hieu0902/Digital-Logic-Final/7408.jpg

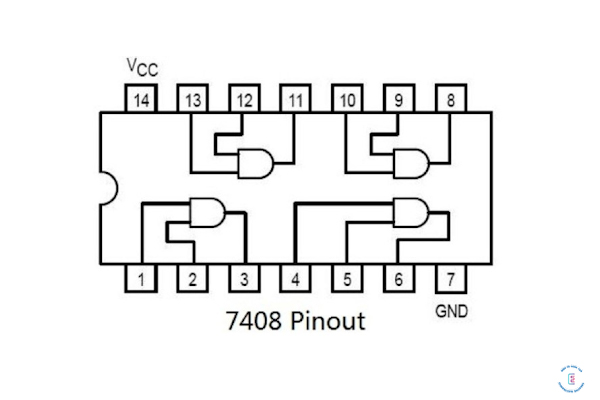
7408.jpg
