hieu0902/Digital-Logic-Final/7410.gif

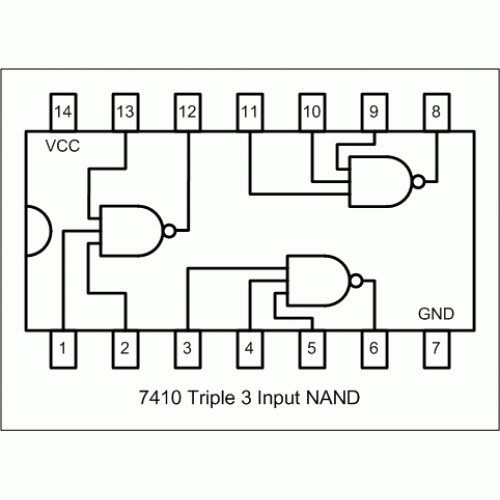
7410.gif
