hieu0902/Digital-Logic-Final/7411.png

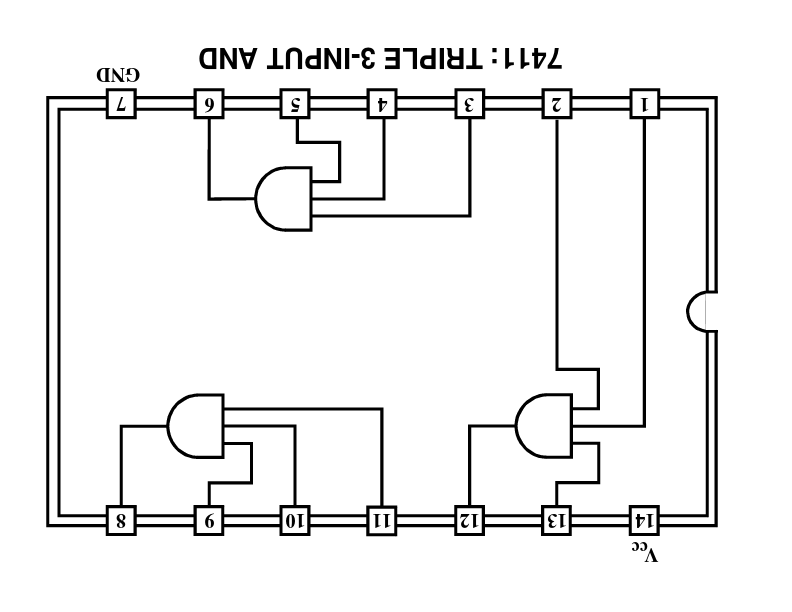
7411.png
