hieu0902/Digital-Logic-Final/7414.png

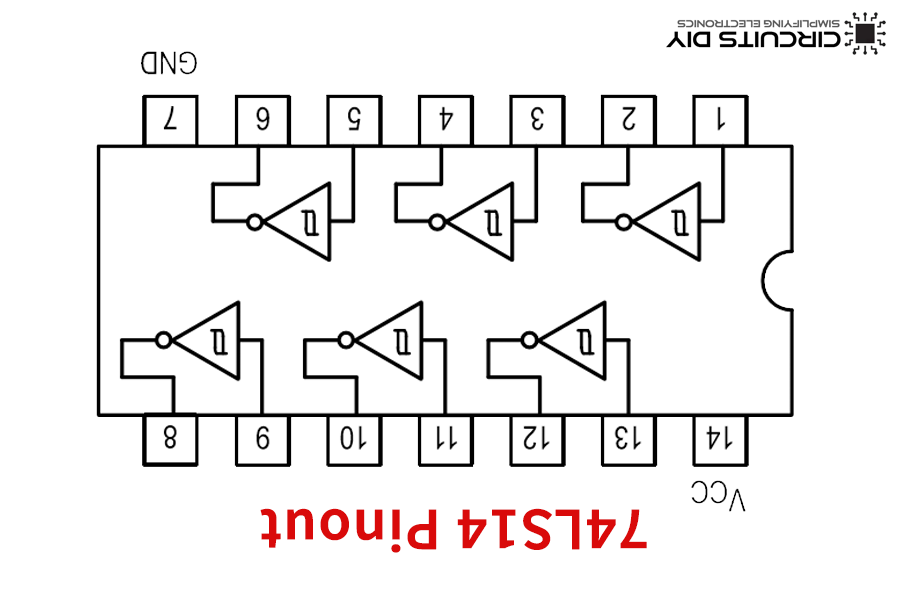
7414.png
