hieu0902/Digital-Logic-Final/7432.png

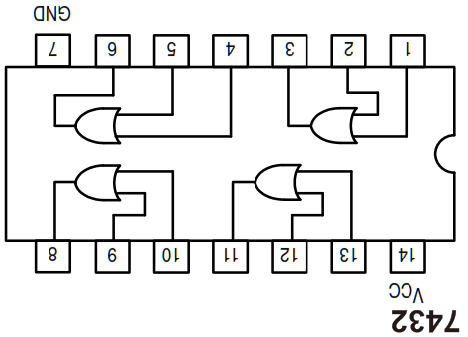
7432.png
