hieu0902/Digital-Logic-Final/7486.jpg

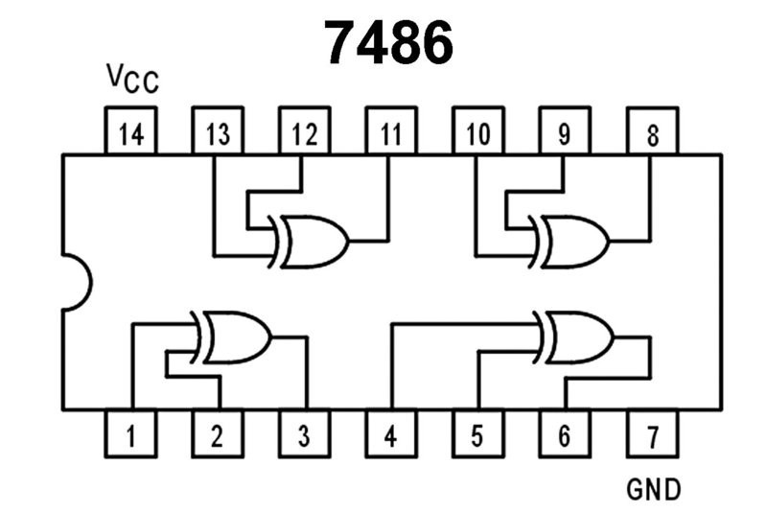
7486.jpg
