hieu0902/Digital-Logic-Final/74157.png

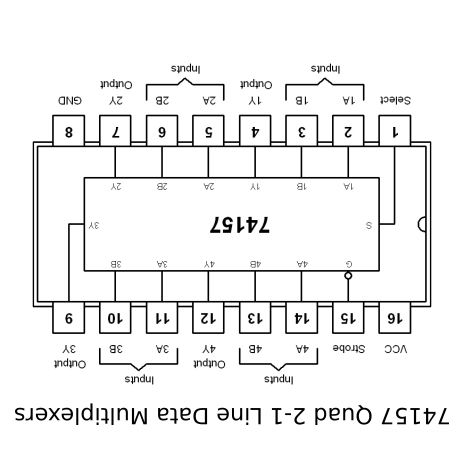
74157.png
